JulienChvt/Microcontroller_Open_Source_Hardware/KiCAD/Kicad_Shield_Schmitt_Trigger/3D visualisation (front)(1).png

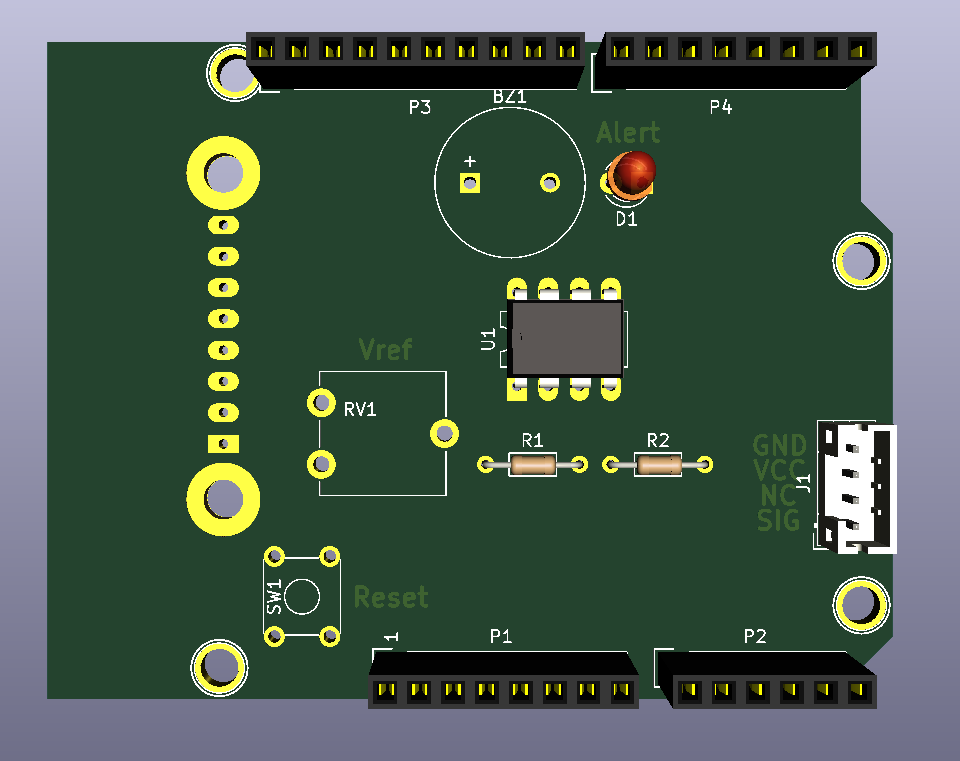
KiCAD/Kicad_Shield_Schmitt_Trigger/3D visualisation (front)(1).png
